ArturChechui/esp_radio/components/common/include/Dumpers.hpp

/**
 * @file Dumpers.hpp
 * @brief Utility functions for converting system types and events to strings.
 *
 * This file contains inline helper functions to "dump" internal enums and
 * event structures into human-readable strings, primarily for logging and
 * diagnostic purposes.
 */

#pragma once
#include <string>

#include "Events.hpp"
#include "Overloaded.hpp"
#include "Types.hpp"

namespace common {
/**
 * @brief Converts a Button enum value to its string representation.
 * @param b The button enum to convert.
 * @return A string such as "PlayStop", "Next", or "Previous".
 */
inline std::string dump(const Button& b) {
    switch (b) {
        case Button::PlayStop:
            return "PlayStop";
        case Button::Next:
            return "Next";
        case Button::Previous:
            return "Previous";
        default:
            return "Unknown";
    }
}

/**
 * @brief Converts a PlaybackStatus enum value to its string representation.
 * @param p The playback status to convert.
 * @return A string such as "Playing", "Buffering", or "Stopped".
 */
inline std::string dump(const PlaybackStatus& p) {
    switch (p) {
        case PlaybackStatus::Playing:
            return "Playing";
        case PlaybackStatus::Buffering:
            return "Buffering";
        case PlaybackStatus::Stopped:
            return "Stopped";
        case PlaybackStatus::Idle:
            return "Idle";
        case PlaybackStatus::Error:
            return "Error";
        default:
            return "Unknown";
    }
}

/**
 * @brief Converts an Icon enum value to its string representation.
 * @param i The icon enum to convert.
 * @return A human-readable name of the icon.
 */
inline std::string dump(const Icon& i) {
    switch (i) {
        case Icon::WifiOff:
            return "WifiOff";
        case Icon::Wifi1:
            return "Wifi1";
        case Icon::Wifi2:
            return "Wifi2";
        case Icon::Wifi3:
            return "Wifi3";
        case Icon::Play:
            return "Play";
        case Icon::Buffering:
            return "Buffering";
        case Icon::Stop:
            return "Stop";
        case Icon::BatteryLow:
            return "BatteryLow";
        case Icon::BatteryMid:
            return "BatteryMid";
        case Icon::BatteryFull:
            return "BatteryFull";
        case Icon::Volume0:
            return "Volume0";
        case Icon::Volume1:
            return "Volume1";
        case Icon::Volume2:
            return "Volume2";
        case Icon::Volume3:
            return "Volume3";
        case Icon::Volume4:
            return "Volume4";
        case Icon::Volume5:
            return "Volume5";
        default:
            return "Unknown";
    }
}

/**
 * @brief Converts a StationData struct value to its string representation.
 * @param s The StationData struct to convert.
 * @return A string such as "{name=STATION1}"
 */
inline std::string dump(const StationData& s) {
    std::string out;
    out.reserve(8 + s.name.size() + 1);
    out += "{name=";
    out += s.name;
    out += "}";
    return out;
}

/**
 * @brief Converts a TaskHandle struct value to its string representation.
 * @param t The TaskHandle struct to convert.
 * @return A string such as "{runId=1,slot=2}"
 */
inline std::string dump(const TaskHandle& t) {
    std::string out;
    out.reserve(24);  // enough for "{runId=65535,slot=65535}"
    out += "{runId=";
    out += std::to_string(t.runId);
    out += ",slot=";
    out += std::to_string(t.slot);
    out += "}";
    return out;
}

/**
 * @brief Converts an AppEvent variant to a detailed string representation.
 * * Uses std::visit and the Overloaded pattern to inspect the specific event type
 * and extract its internal fields into a formatted string.
 * * @param ev The application event to dump.
 * @return A string containing the event type and its parameters.
 */
inline std::string dump(const common::AppEvent& ev) {
    return std::visit(
        Overloaded{
            [](const ButtonPressedEvent& e) {
                return "ButtonPressedEvent{b=" + dump(e.button) + "}";
            },
            [](const ButtonLongPressedEvent& e) {
                return "ButtonLongPressedEvent{b=" + dump(e.button) + "}";
            },
            [](const PlaybackStatusChangedEvent& e) {
                return "PlaybackStatusChangedEvent{s=" + dump(e.status) + "}";
            },
            [](const TempHumidUpdateEvent& e) {
                return "TempHumidUpdateEvent{t=" + std::to_string(e.temperature) +
                       ", h=" + std::to_string(e.humidity) + "}";
            },
            [](const LightLevelUpdateEvent& e) {
                return std::string("LightLevelUpdateEvent{lux=") + std::to_string(e.lux) + "}";
            },
            [](const BatteryLevelUpdateEvent& e) {
                return std::string("BatteryLevelUpdateEvent{mv=") + std::to_string(e.millivolts) +
                       ", p=" + std::to_string(e.percent) + "}";
            },
            [](const SystemInitedEvent&) { return std::string("SystemInitedEvent{}"); },
            [](const ClapFeatureStateChangedEvent& c) {
                return std::string("ClapFeatureStateChangedEvent{e=") +
                       (c.isEnabled ? "true}" : "false}");
            },
            [](const CurrentStationChangedEvent&) {
                return std::string{"CurrentStationChangedEvent{}"};
            },
            [](const WifiStateChangedEvent& e) {
                return std::string("WifiStateChangedEvent{c=") +
                       (e.isConnected ? "true, b=" : "false, b=") + std::to_string(e.bars) + "}";
            },
            [](const VolumeChangedEvent& e) {
                return std::string("VolumeChangedEvent{v=") + std::to_string(e.volume) + "}";
            },
            [](const SwitchToWifiProvScreenEvent&) {
                return std::string("SwitchToWifiProvScreenEvent{}");
            },
            [](const SwitchToSyncInProgressScreenEvent&) {
                return std::string("SwitchToSyncInProgressScreenEvent{}");
            },
            [](const SwitchToMainScreenEvent&) { return std::string("SwitchToMainScreenEvent{}"); },
            [](const WifiCredsReceivedEvent& e) { return std::string("WifiCredsReceivedEvent{}"); },
            [](const auto&) { return std::string{"<unknown event>"}; }},
        ev);
}

}  // namespace common
