ArturChechui/esp_radio/components/adapters/src/I2cBus.cpp

#include "I2cBus.hpp"

#include "BoardConfig.hpp"
#include "LockGuard.hpp"

// IDF
#include <driver/i2c_master.h>
#include <esp_log.h>
#include <freertos/FreeRTOS.h>

namespace adapters {

namespace {
constexpr const char* Tag = "I2cBus";
}  // namespace

I2cBus::I2cBus() : mBusHandle(nullptr), mFreqHz(common::I2C_FREQ_HZ), mMutex() {
    ESP_LOGI(Tag, "Creating I2cBus");
}

I2cBus::~I2cBus() {
    ESP_LOGI(Tag, "I2C cleanup: %zu device(s), bus %s", mDeviceHandles.size(),
             mBusHandle ? "valid" : "null");

    for (auto& [addr, devHandle] : mDeviceHandles) {
        (void)addr;
        if (devHandle) {
            i2c_master_bus_rm_device(devHandle);
        }
    }
    mDeviceHandles.clear();

    if (mBusHandle) {
        i2c_del_master_bus(mBusHandle);
        mBusHandle = nullptr;
    }
}

bool I2cBus::init() {
    common::LockGuard guard(mMutex);

    if (mBusHandle) {
        ESP_LOGW(Tag, "I2C bus already configured");
        return true;
    }

    i2c_master_bus_config_t busConfig = {};
    busConfig.i2c_port = I2C_NUM_0;
    busConfig.sda_io_num = static_cast<gpio_num_t>(common::I2C_SDA_GPIO);
    busConfig.scl_io_num = static_cast<gpio_num_t>(common::I2C_SCL_GPIO);
    busConfig.clk_source = I2C_CLK_SRC_DEFAULT;
    busConfig.flags.enable_internal_pullup = true;

    const esp_err_t ret = i2c_new_master_bus(&busConfig, &mBusHandle);
    if (ret == ESP_OK) {
        ESP_LOGI(Tag, "I2C master bus configured (SDA=%d, SCL=%d, freq=%lu Hz)",
                 common::I2C_SDA_GPIO, common::I2C_SCL_GPIO, static_cast<unsigned long>(mFreqHz));
        return true;
    }

    ESP_LOGE(Tag, "Failed to configure I2C master bus: %s", esp_err_to_name(ret));
    return false;
}

bool I2cBus::writeBytes(const uint8_t deviceAddr, const uint8_t* data, const size_t len,
                        const uint32_t timeoutMs) {
    common::LockGuard guard(mMutex);

    if (!mBusHandle) {
        ESP_LOGE(Tag, "I2C bus not initialized");
        return false;
    }
    if (!data || len == 0) {
        return false;
    }

    const TickType_t ticks = pdMS_TO_TICKS(timeoutMs);

    auto transmit = [&](i2c_master_dev_handle_t dev) -> esp_err_t {
        return i2c_master_transmit(dev, data, len, ticks);
    };

    i2c_master_dev_handle_t devHandle = getOrCreateDeviceHandle(deviceAddr);
    if (!devHandle) {
        ESP_LOGE(Tag, "Failed to get/create device handle for 0x%02X", deviceAddr);
        return false;
    }

    esp_err_t ret = transmit(devHandle);
    if (ret == ESP_OK) {
        return true;
    }

    ESP_LOGW(Tag, "I2C write failed to 0x%02X: %s (len=%u)", deviceAddr, esp_err_to_name(ret),
             static_cast<unsigned>(len));

    // TODO: Adapter shouldn't have any business logic with the retry etc, it has to be handled by
    // the services, so for now it is commented if works fine, it will be removed
    // One retry path: drop handle, recreate, retry.
    // if (ret == ESP_ERR_INVALID_STATE || ret == ESP_FAIL) {
    //     auto it = mDeviceHandles.find(deviceAddr);
    //     if (it != mDeviceHandles.end()) {
    //         if (it->second) {
    //             i2c_master_bus_rm_device(it->second);
    //         }
    //         mDeviceHandles.erase(it);
    //         ESP_LOGI(Tag, "Dropped device handle for 0x%02X", deviceAddr);
    //     }
    //
    //     devHandle = getOrCreateDeviceHandle(deviceAddr);
    //     if (!devHandle) {
    //         return false;
    //     }
    //
    //     ret = transmit(devHandle);
    //     if (ret == ESP_OK) {
    //         return true;
    //     }
    //
    //     ESP_LOGW(Tag, "I2C retry failed to 0x%02X: %s", deviceAddr, esp_err_to_name(ret));
    // }

    return false;
}

bool I2cBus::readBytes(const uint8_t deviceAddr, uint8_t* data, const size_t len,
                       const uint32_t timeoutMs) {
    common::LockGuard guard(mMutex);

    if (!mBusHandle) {
        ESP_LOGE(Tag, "I2C bus not initialized");
        return false;
    }
    if (!data || len == 0UL) {
        return false;
    }

    i2c_master_dev_handle_t devHandle = getOrCreateDeviceHandle(deviceAddr);
    if (!devHandle) {
        ESP_LOGE(Tag, "Failed to get/create device handle for 0x%02X", deviceAddr);
        return false;
    }

    const esp_err_t ret = i2c_master_receive(devHandle, data, len, pdMS_TO_TICKS(timeoutMs));
    if (ret != ESP_OK) {
        ESP_LOGW(Tag, "I2C read failed from 0x%02X: %s", deviceAddr, esp_err_to_name(ret));
    }

    return (ret == ESP_OK);
}

i2c_master_dev_handle_t I2cBus::getOrCreateDeviceHandle(const uint8_t deviceAddr) {
    auto it = mDeviceHandles.find(deviceAddr);
    if (it != mDeviceHandles.end()) {
        return it->second;
    }

    i2c_device_config_t devConfig = {};
    devConfig.dev_addr_length = I2C_ADDR_BIT_LEN_7;
    devConfig.device_address = deviceAddr;
    devConfig.scl_speed_hz = mFreqHz;

    i2c_master_dev_handle_t devHandle = nullptr;
    const esp_err_t ret = i2c_master_bus_add_device(mBusHandle, &devConfig, &devHandle);

    if (ret == ESP_OK) {
        mDeviceHandles[deviceAddr] = devHandle;
        ESP_LOGI(Tag, "Created device handle for 0x%02X", deviceAddr);
    } else {
        ESP_LOGE(Tag, "Failed to create device handle for 0x%02X: %s", deviceAddr,
                 esp_err_to_name(ret));
    }

    return devHandle;
}

}  // namespace adapters
