ArturChechui/esp_radio/components/common/include/IBinarySemaphore.hpp

#pragma once

#include <cstdint>

namespace common {
class IBinarySemaphore {
   public:
    virtual ~IBinarySemaphore() = default;

    virtual bool wait(const uint32_t& timeoutMs) const = 0;
    virtual void signal() = 0;
    virtual bool isValid() const = 0;
    virtual void reset() = 0;
};

}  // namespace common
